DeMarco/DMH-Output/DMH_Output_PCB_Mezanine/faca_caber.jpg

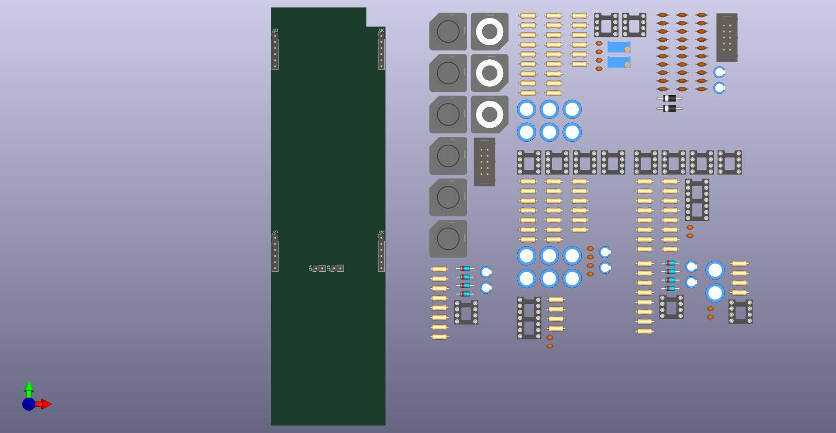
DMH_Output_PCB_Mezanine/faca_caber.jpg
