DeMarco/DMH-Output/Images/controls_back.png

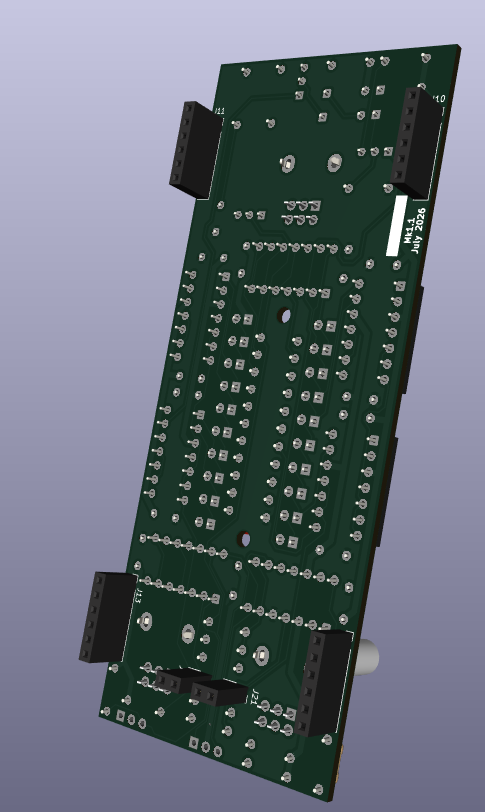
Images/controls_back.png
