DeMarco/DMH-Output/Images/main_front.png

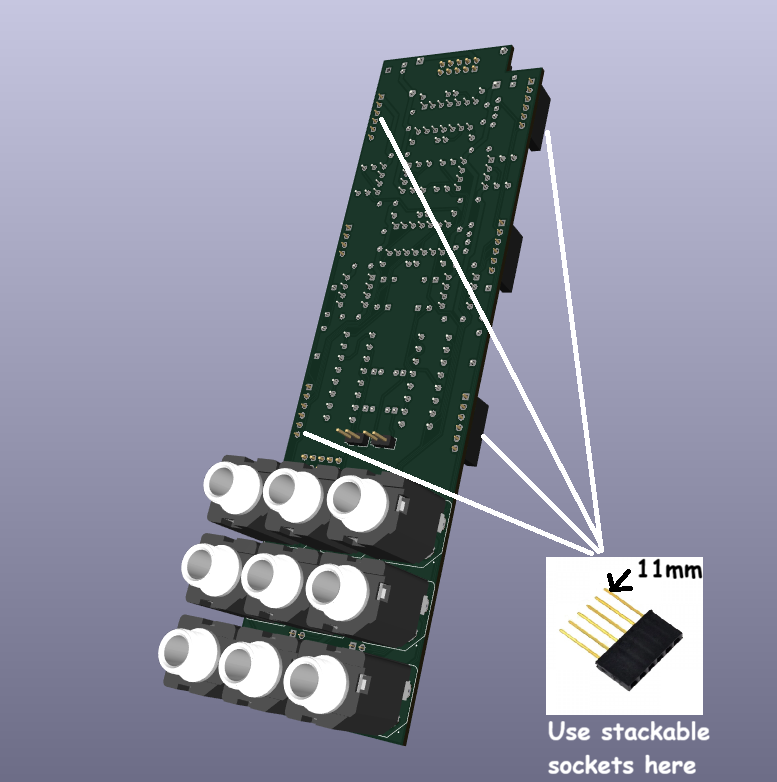
Images/main_front.png
